reivax-boucoi/Electronic_Load/screenshots/mainmenu.jpg

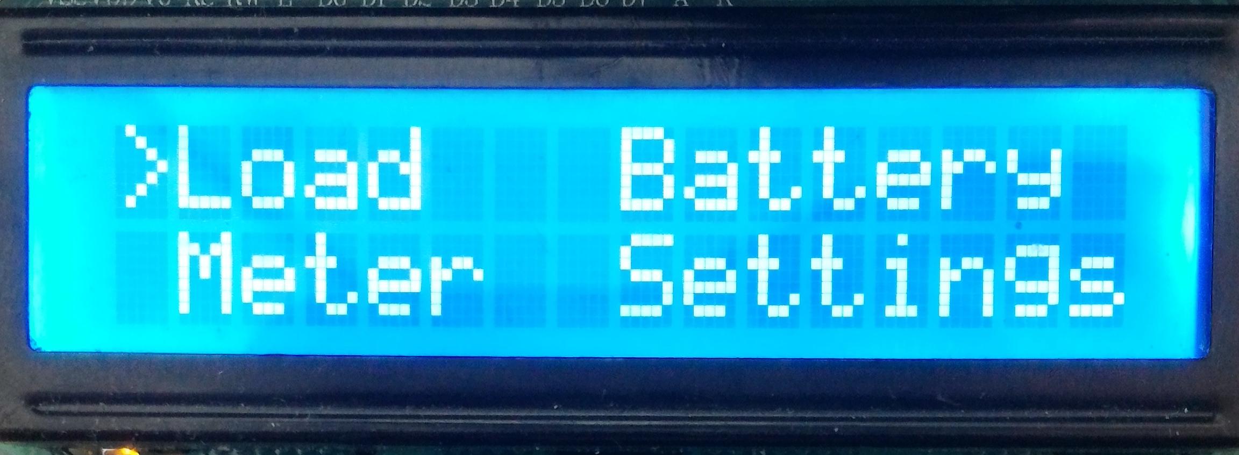
screenshots/mainmenu.jpg
