reivax-boucoi/Electronic_Load/screenshots/screen_cc.jpg

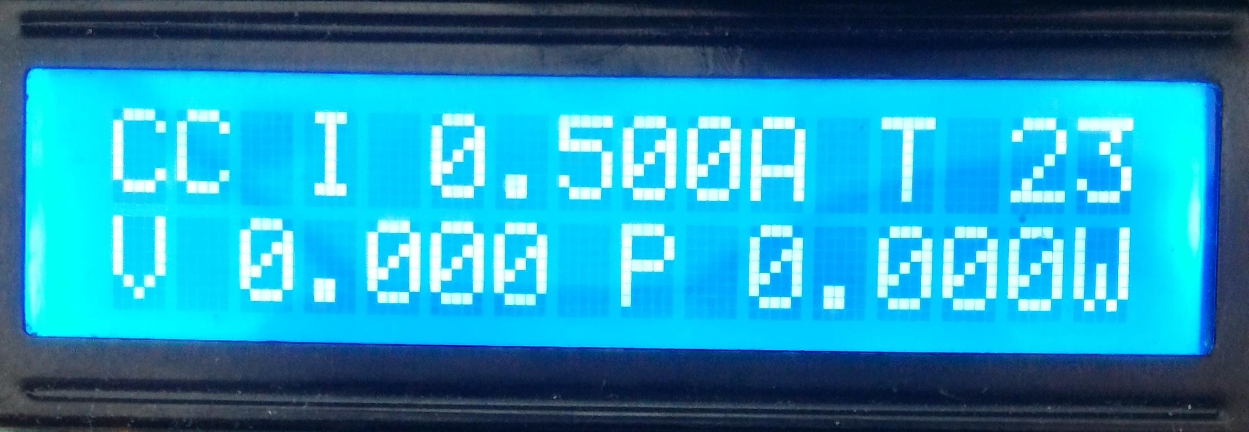
screenshots/screen_cc.jpg
