reivax-boucoi/Electronic_Load/screenshots/screen_settings.jpg

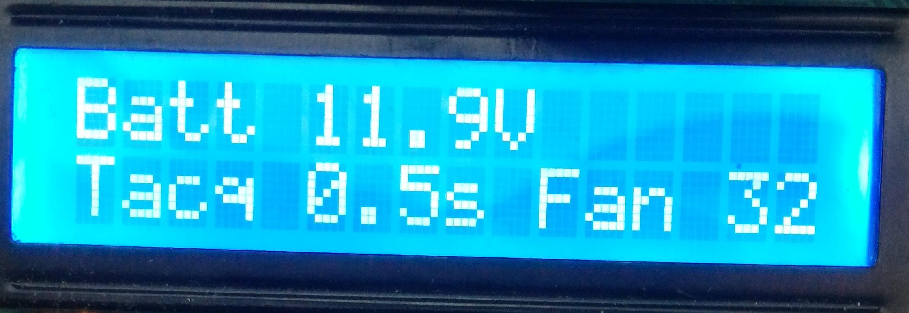
screenshots/screen_settings.jpg
