reivax-boucoi/Electronic_Load/screenshots/top_bareboard.jpg

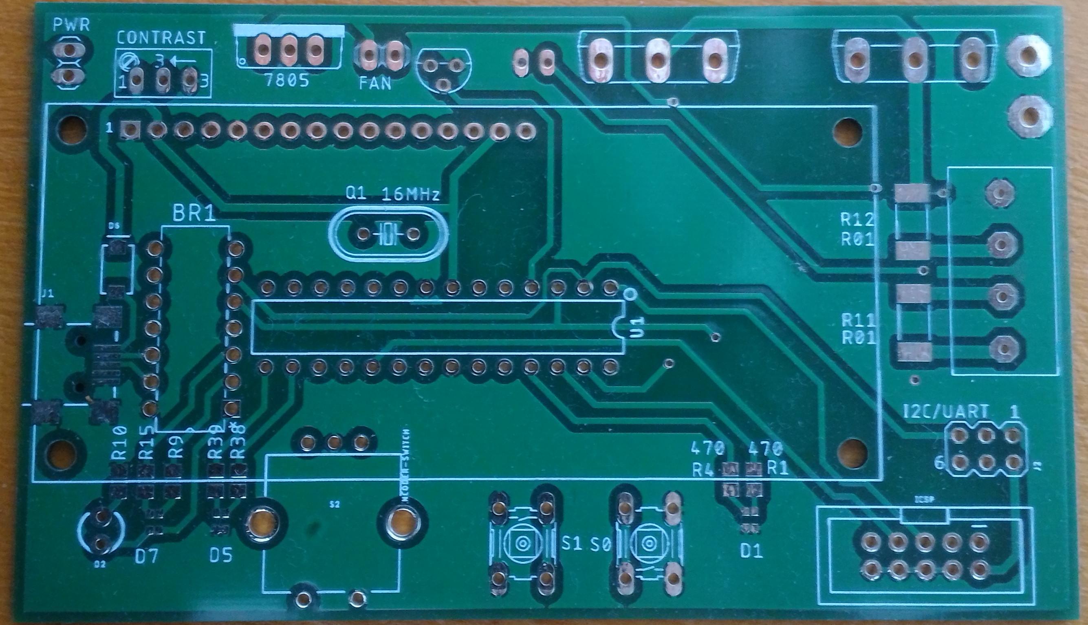
screenshots/top_bareboard.jpg
