reivax-boucoi/Electronic_Load/screenshots/bottom_assembled.jpg

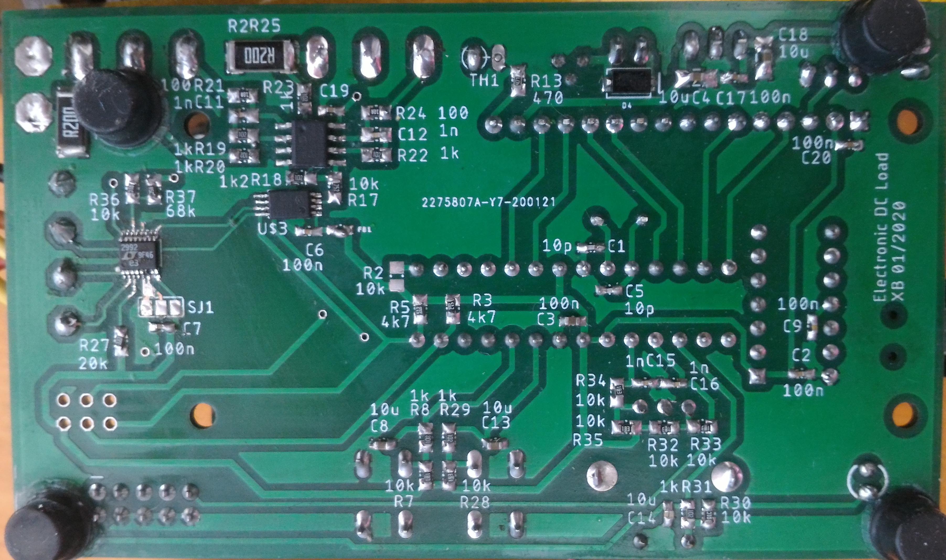
screenshots/bottom_assembled.jpg
