reivax-boucoi/Electronic_Load/firmware/Load.h

#ifndef LOAD_H
#define LOAD_H

#include <Arduino.h>
#include <Wire.h>
#include "Utils.h"


#ifdef BOARD1

#define DAC_CAL_COEFF 728.0//730.0 // Iout=2*Vref*DACVal/4096/.2*R1/(R1+R2), DACVal=Iout*.2*4096/2/Vref*(R1+R2)/R1
#define DAC_OFFSET 0.00

#else

#define DAC_CAL_COEFF 792.0//730.0 // Iout=2*Vref*DACVal/4096/.2*R1/(R1+R2), DACVal=Iout*.2*4096/2/Vref*(R1+R2)/R1
#define DAC_OFFSET 0.003

#endif

#define DAC_ADDR   0x61

#define DAC_REG    0x00
#define VREF_REG   0x08
#define PD_REG     0x09
#define GAIN_REG   0x0A
#define WL_REG     0x0B
#define NVDAC_REG  0x10
#define NVVREF_REG 0x18
#define NVPD_REG   0x19
#define NVGAIN_REG 0x20

#define LEDR2_PIN A2
#define LEDB2_PIN A3
#define FAN_PIN 2

#define TEMP_MAX    40.0
#define FAN_HYST    2.0

extern float fan_temp;

class Load {
  public:
    void init(void);
    void regulate(float current, float temp);
    void on(float current);
    void set(float current);
    void off(void);
    bool onState;
    bool fault=false;

  private:
    void DAC_set(void);
    void DAC_on(void);
    void DAC_off(void);
    float setCurrent;
    uint16_t actualDACVal;
    bool fan_on=false;
};

#endif
